tebl/C64-XUM1541-II/gallery/2021-03-19 00.18.24.jpg

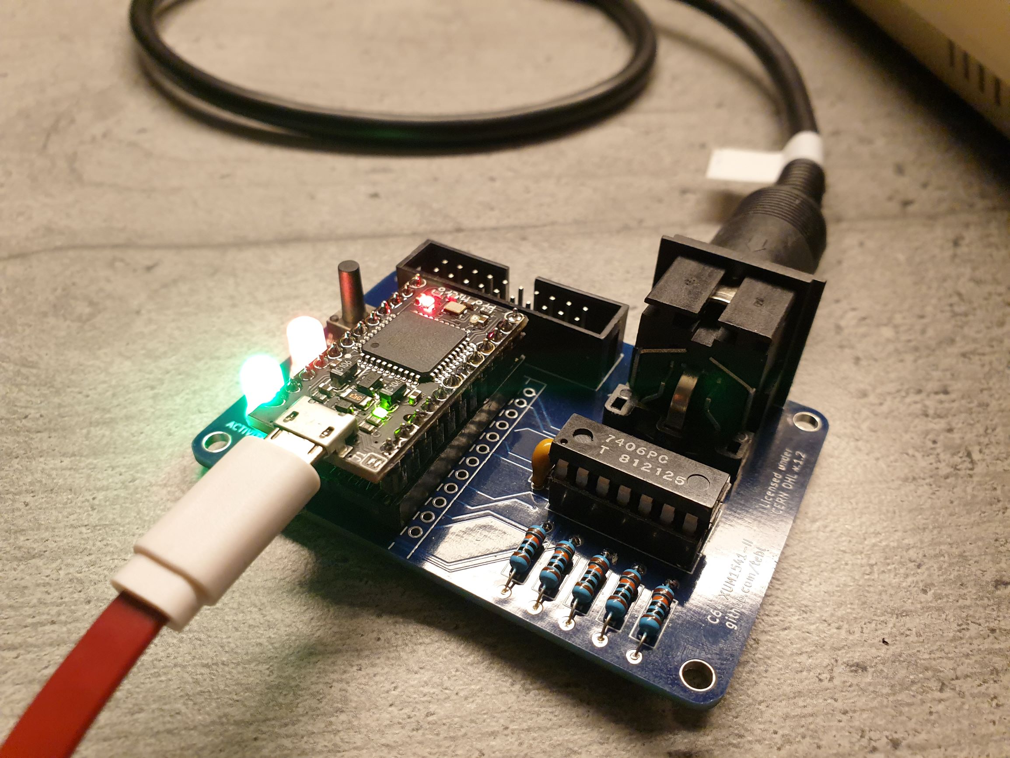
gallery/2021-03-19 00.18.24.jpg
