tebl/C64-XUM1541-II/gallery/2021-03-19 01.20.49.jpg

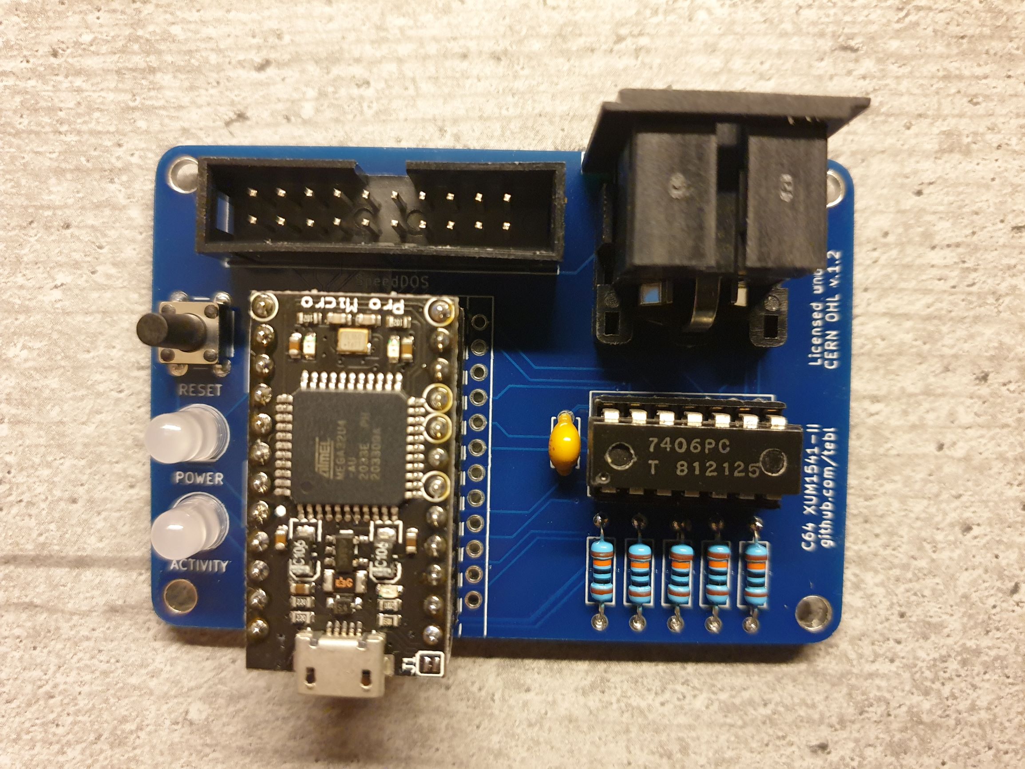
gallery/2021-03-19 01.20.49.jpg
