tebl/C64-XUM1541-II/gallery/2021-04-07 00.23.39.jpg

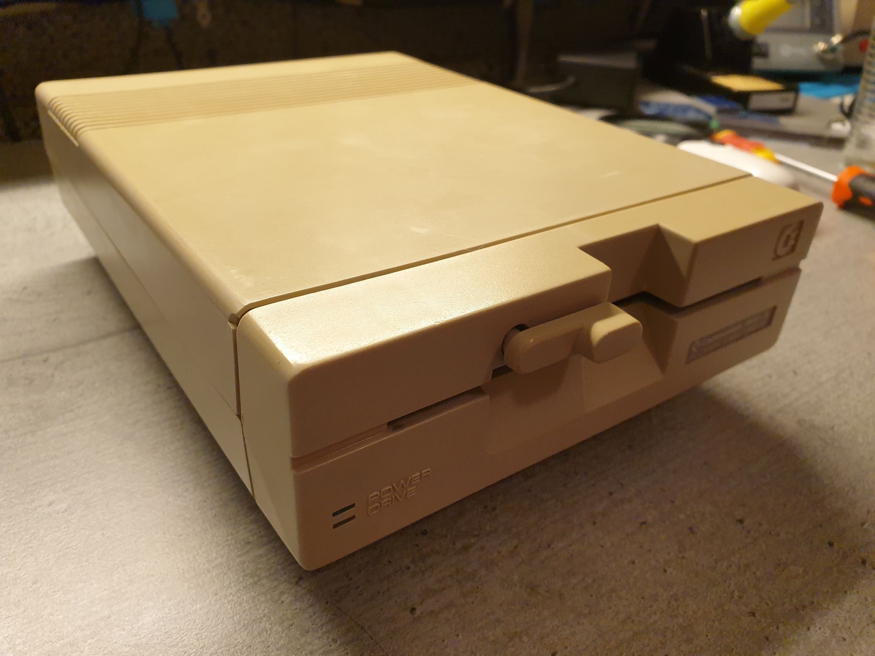
gallery/2021-04-07 00.23.39.jpg
