tebl/C64-XUM1541-II/gallery/2021-04-07 00.24.05.jpg

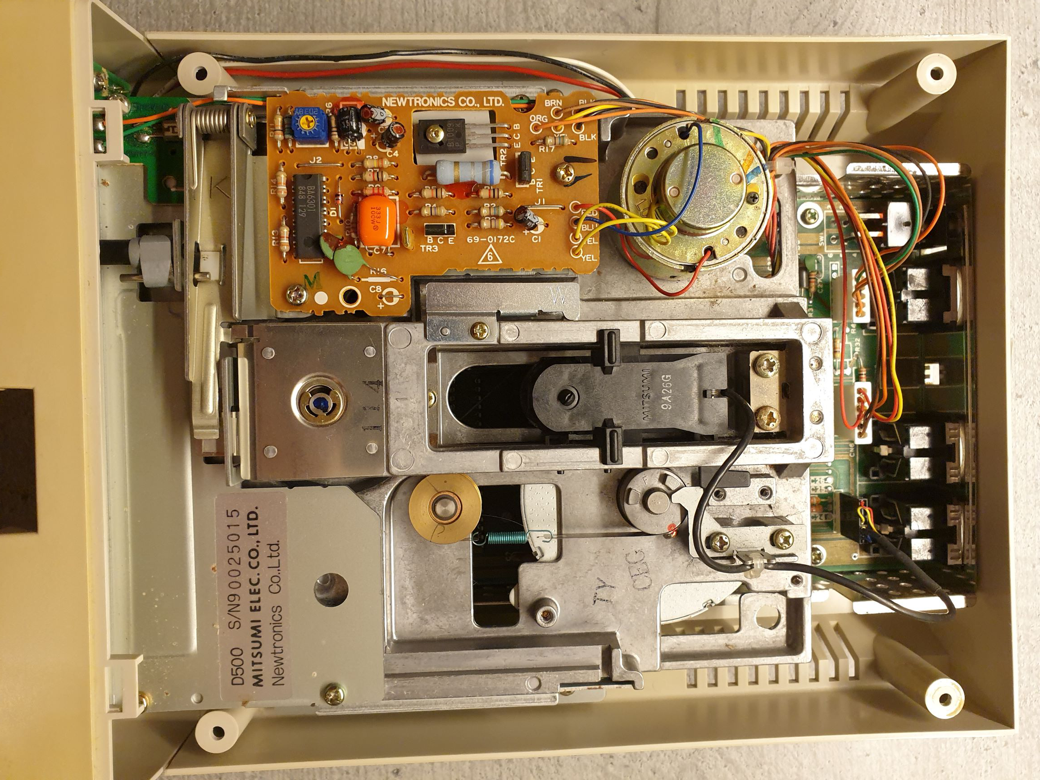
gallery/2021-04-07 00.24.05.jpg
