tebl/C64-XUM1541-II/gallery/2021-04-07 16.45.32.jpg

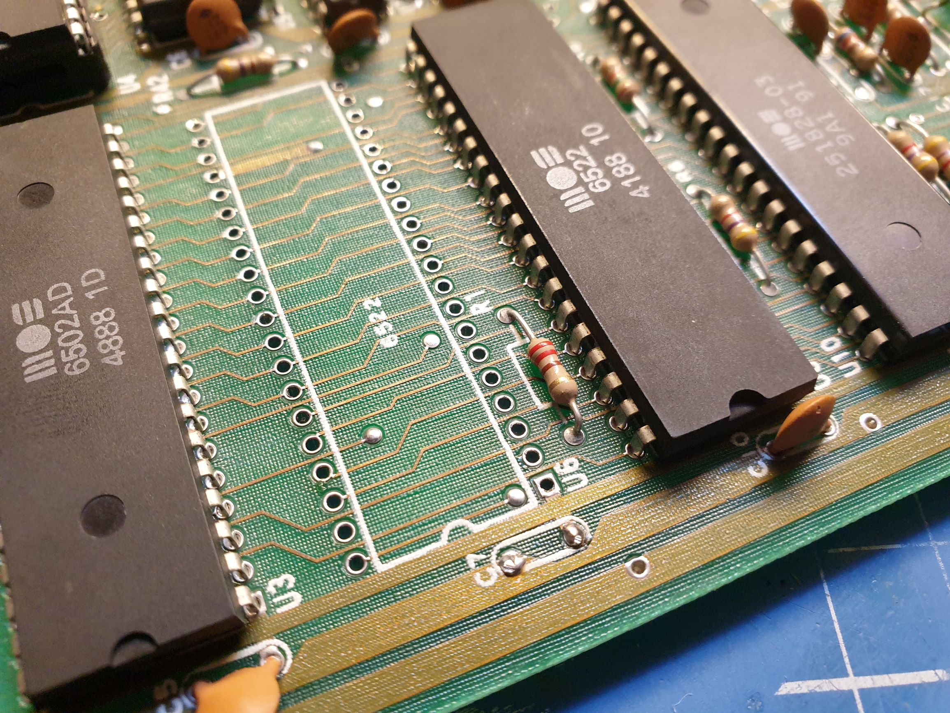
gallery/2021-04-07 16.45.32.jpg
