tebl/C64-XUM1541-II/gallery/2021-04-07 21.13.37.jpg

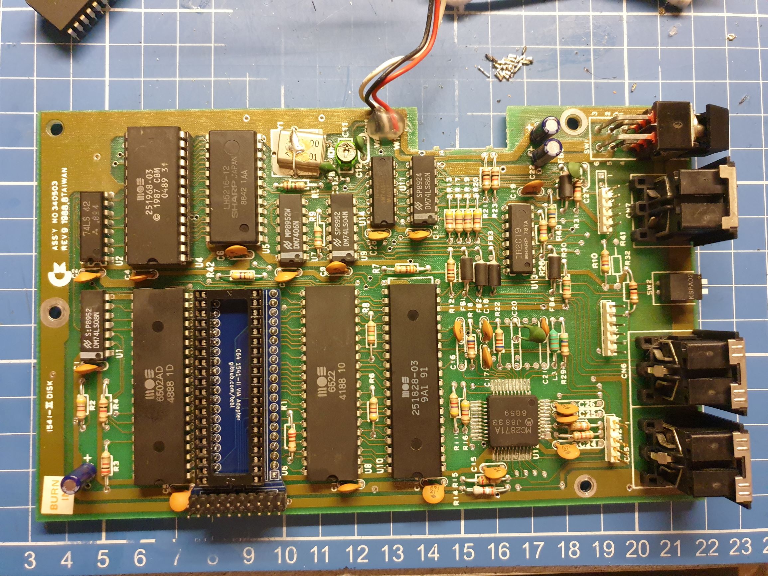
gallery/2021-04-07 21.13.37.jpg
