tebl/C64-XUM1541-II/gallery/2021-04-08 00.27.18.jpg

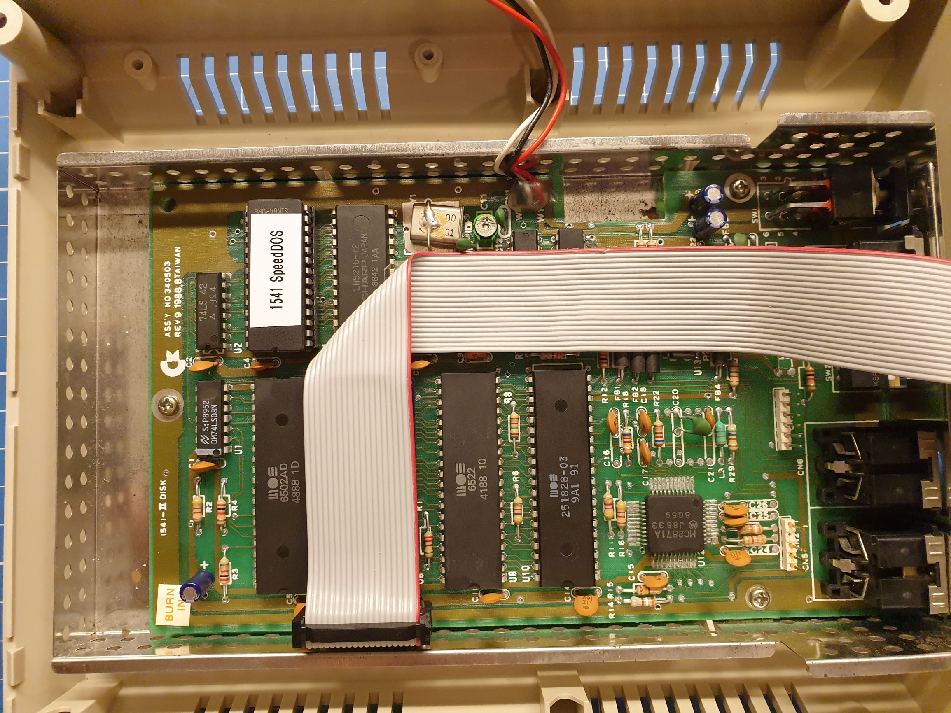
gallery/2021-04-08 00.27.18.jpg
