tebl/C64-XUM1541-II/gallery/2021-04-27 01.16.46.jpg

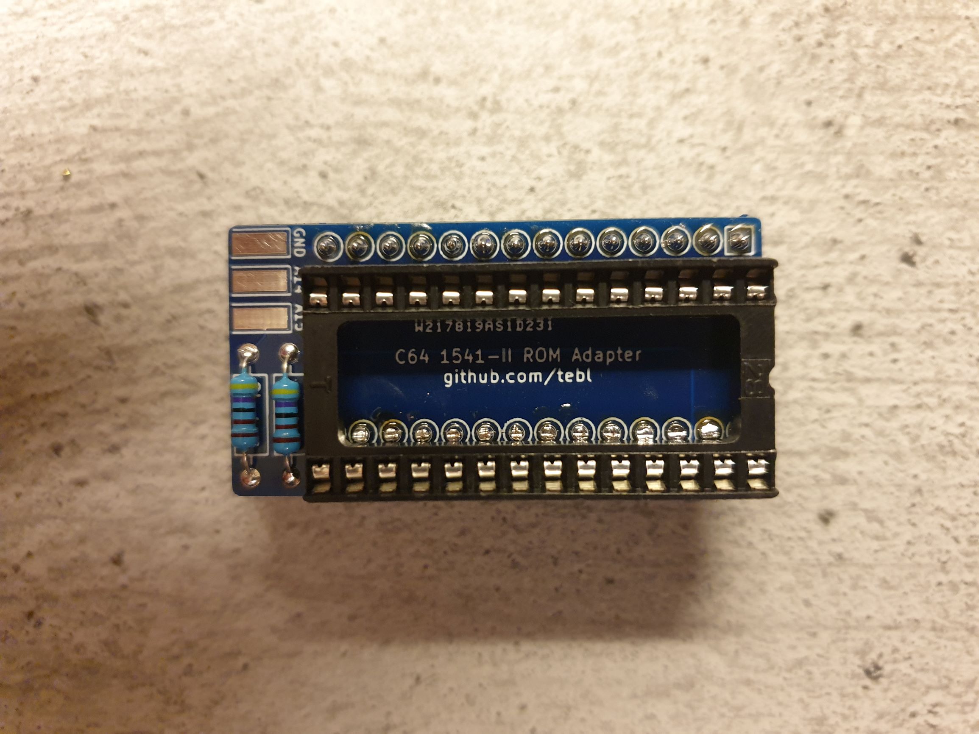
gallery/2021-04-27 01.16.46.jpg
