tebl/C64-XUM1541-II/gallery/2021-05-19 22.53.09.jpg

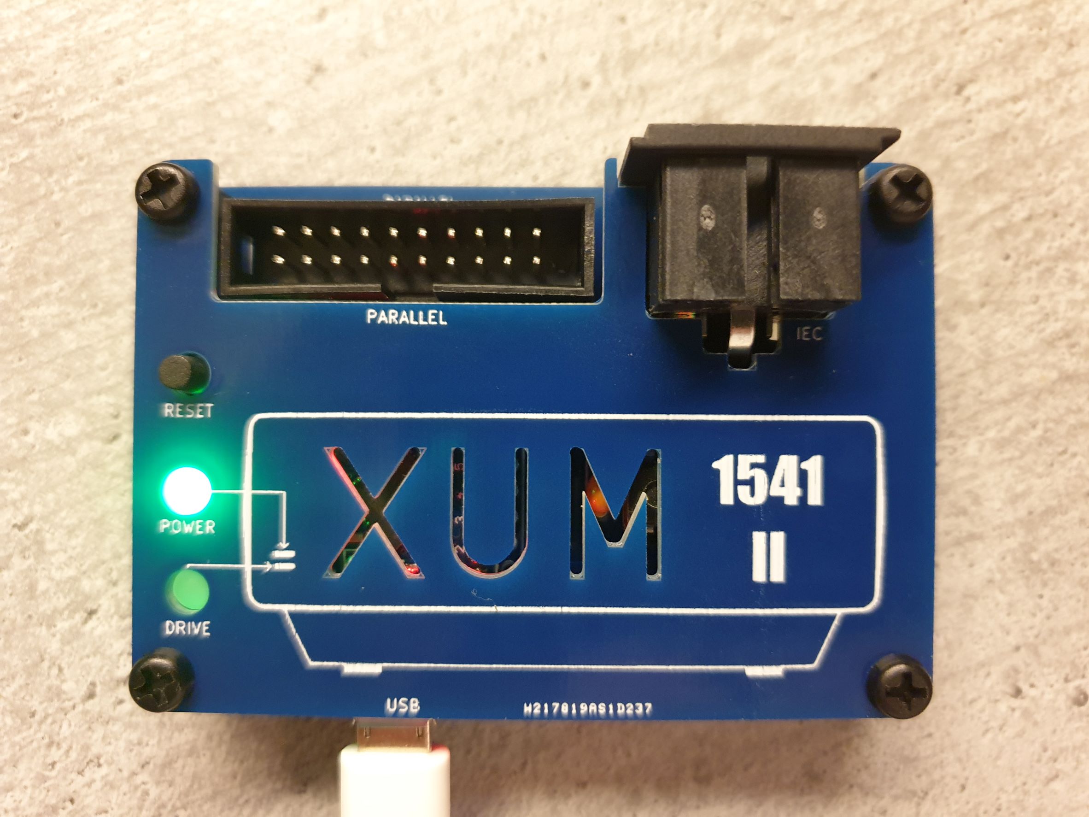
gallery/2021-05-19 22.53.09.jpg
