tebl/C64-XUM1541-II/gallery/C64 1541-II VIA Adapter.png

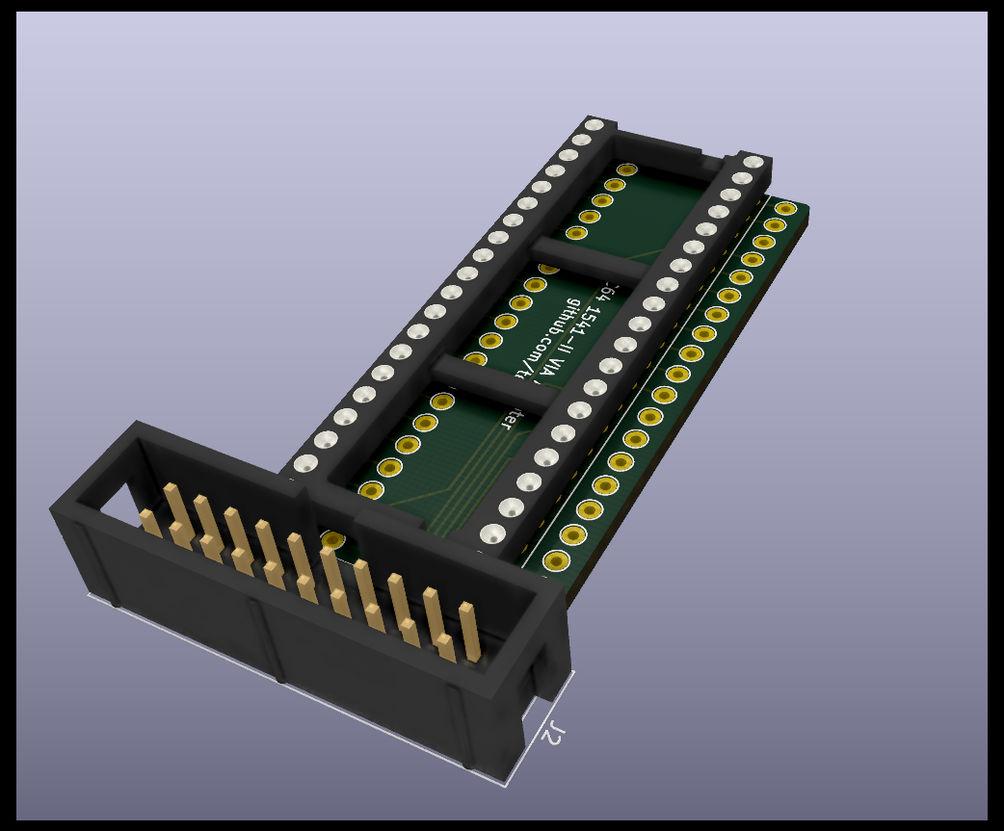
gallery/C64 1541-II VIA Adapter.png
