tebl/C64-XUM1541-II/gallery/C64 SpeedDOS Adapter.png

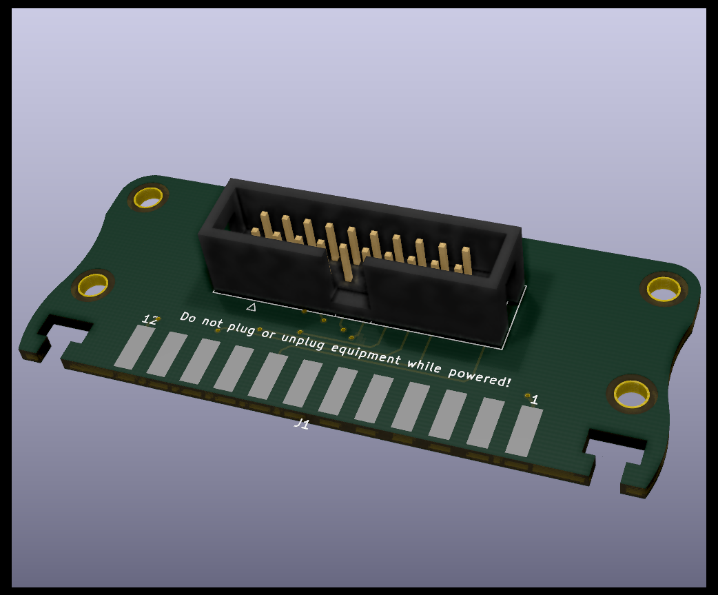
gallery/C64 SpeedDOS Adapter.png
