tebl/C64-XUM1541-II/gallery/C64 XUM1541-II FA1.jpg

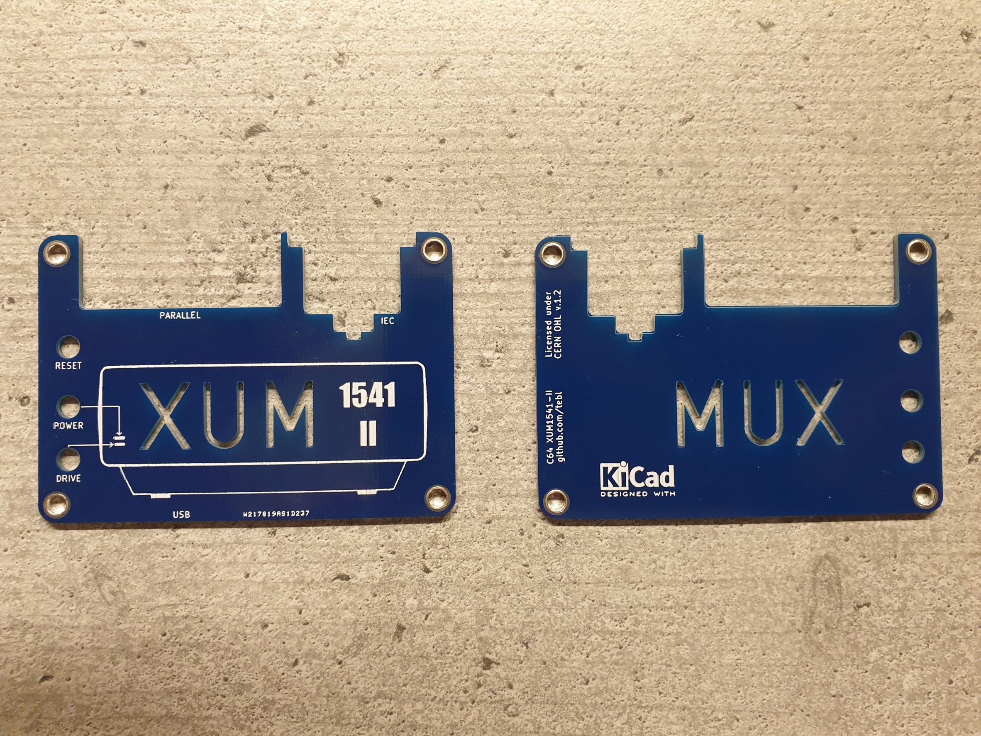
gallery/C64 XUM1541-II FA1.jpg
