tebl/C64-XUM1541-II/gallery/C64 XUM1541-II FA1.png

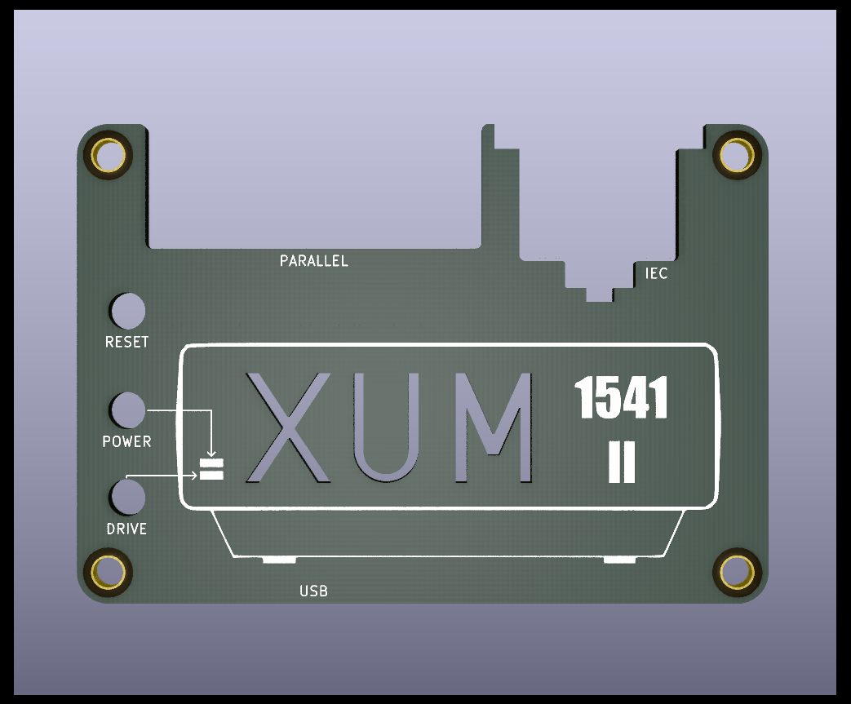
gallery/C64 XUM1541-II FA1.png
