tebl/C64-XUM1541-II/gallery/C64 XUM1541-II FA2.jpg

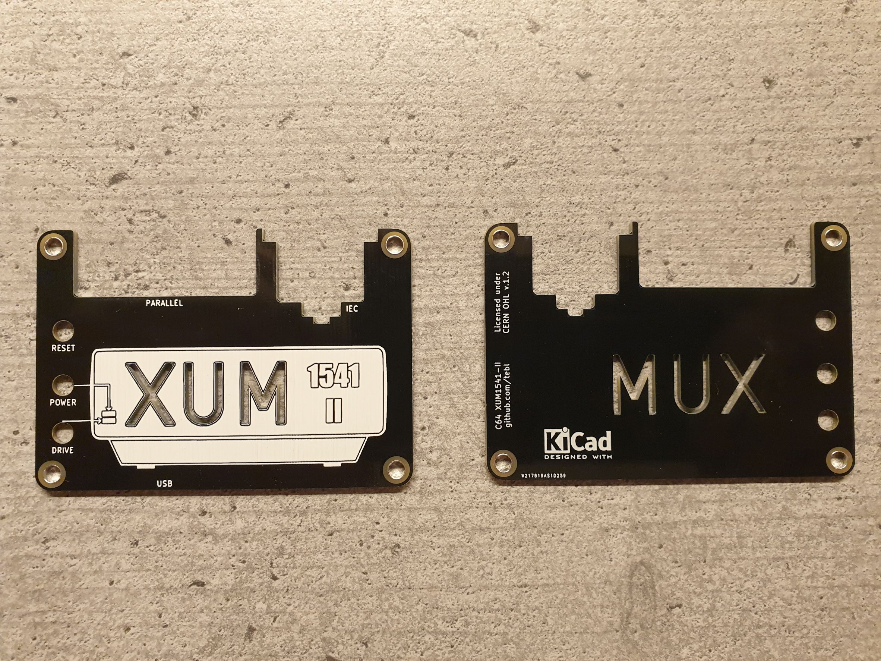
gallery/C64 XUM1541-II FA2.jpg
