tebl/C64-XUM1541-II/gallery/C64 XUM1541-II FA2.png

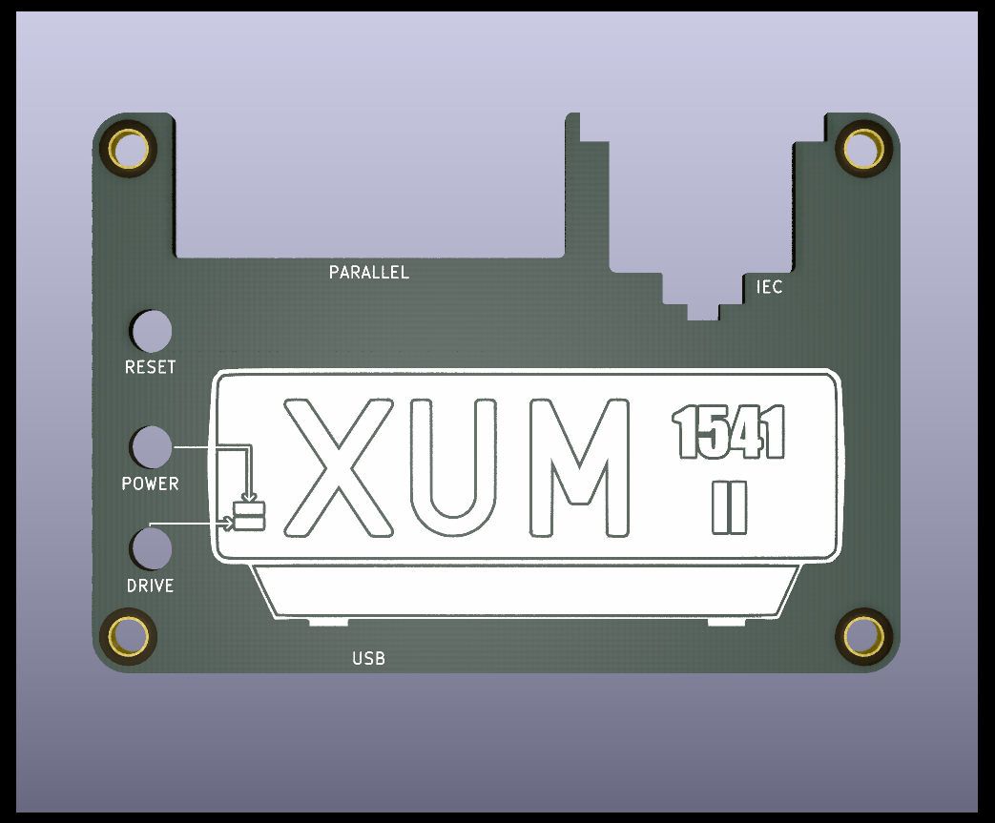
gallery/C64 XUM1541-II FA2.png
