tebl/C64-XUM1541-II/gallery/C64 XUM1541-II.png

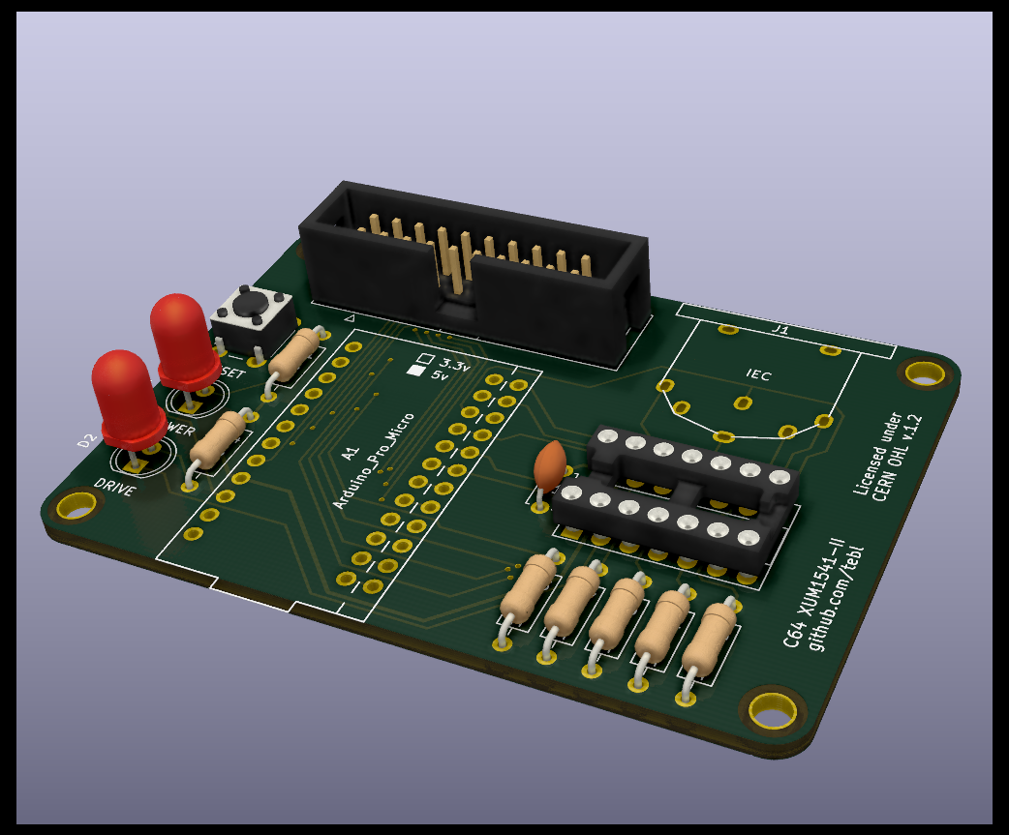
gallery/C64 XUM1541-II.png
