tebl/C64-XUM1541-II/gallery/documentation/zadig001.png

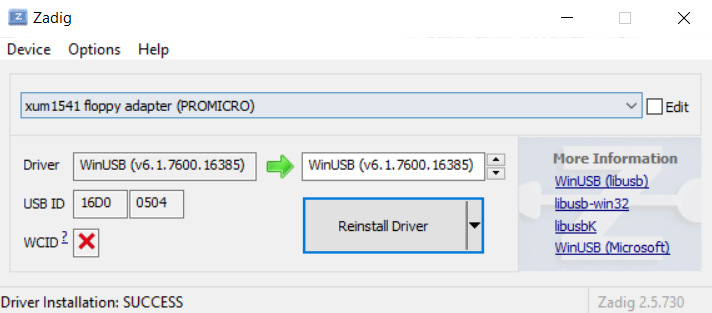
gallery/documentation/zadig001.png
