tebl/C64-XUM1541-II/gallery/documentation/zadig003.png

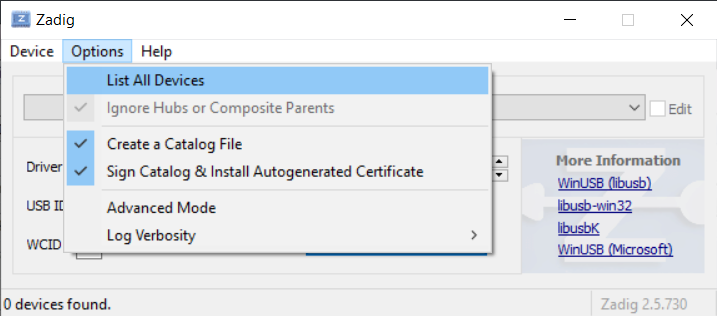
gallery/documentation/zadig003.png
