tebl/C64-XUM1541-II/gallery/build_rom_005.jpg

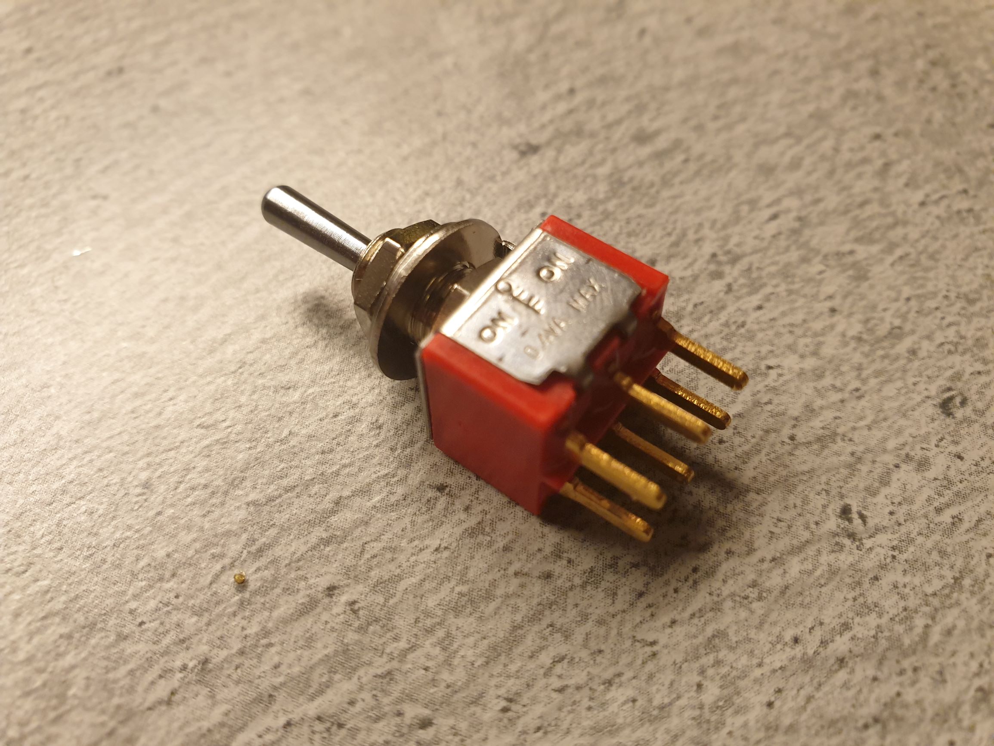
gallery/build_rom_005.jpg
