tebl/C64-XUM1541-II/gallery/build_speeddos_001.jpg

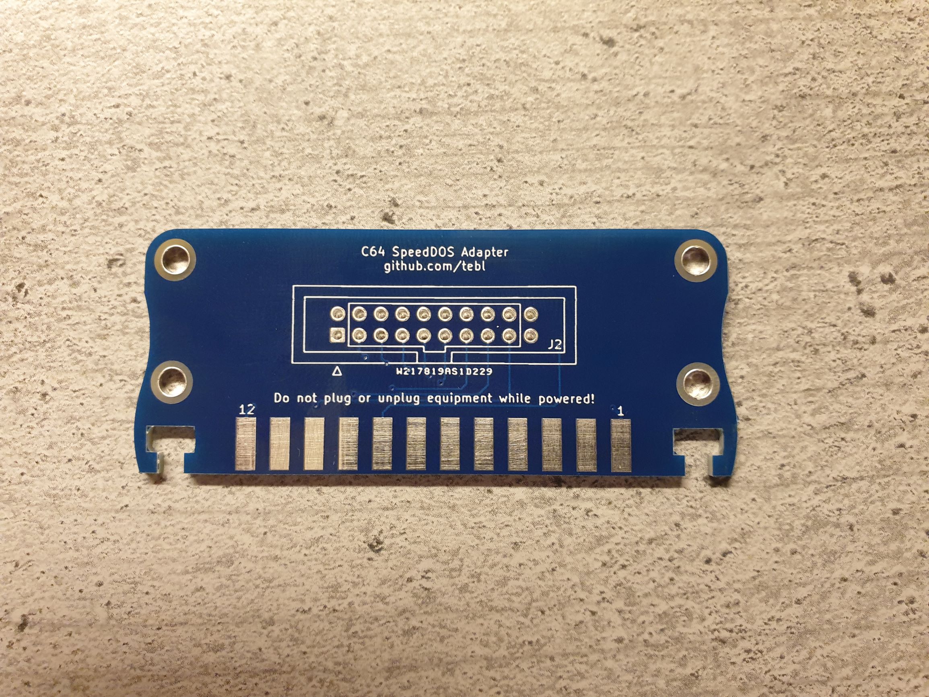
gallery/build_speeddos_001.jpg
